Sidru/Cubet/Images/IMG_20200401_155650.jpg

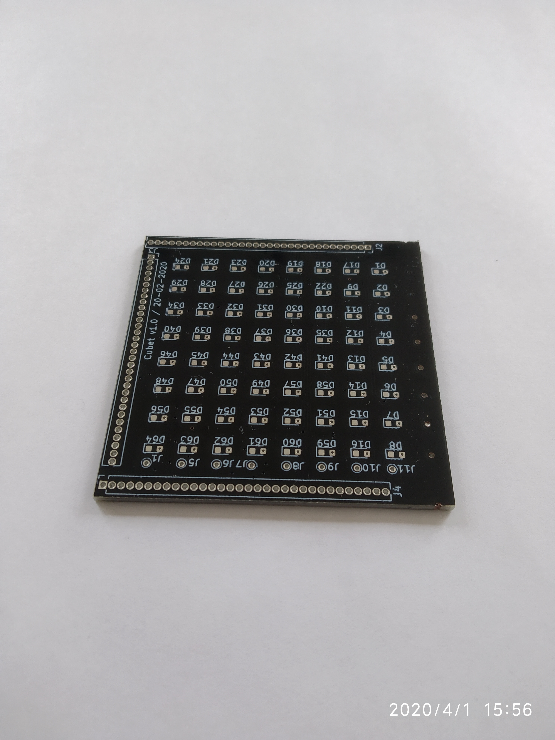
Images/IMG_20200401_155650.jpg
