Sidru/Cubet/Images/IMG_20200401_155713.jpg

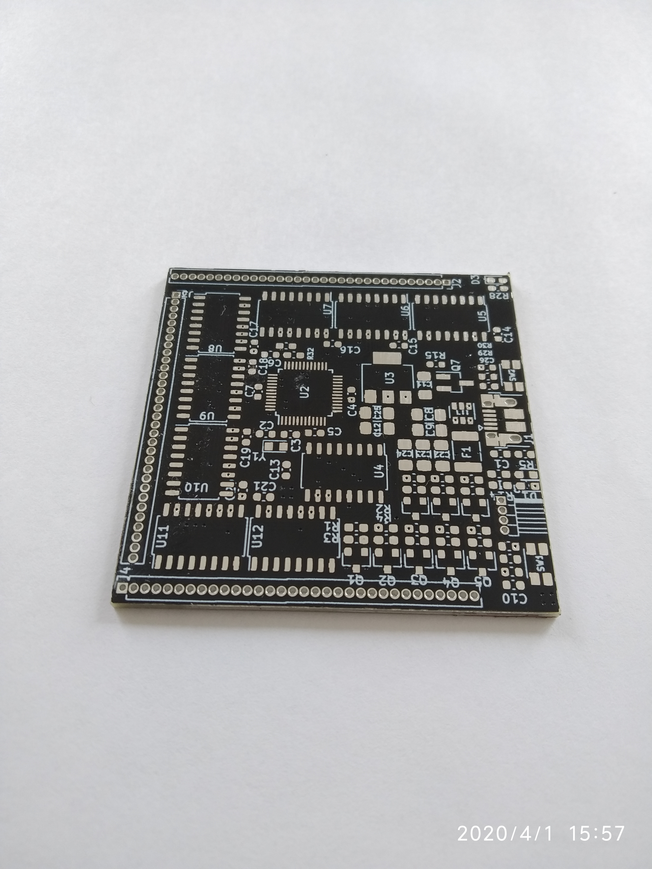
Images/IMG_20200401_155713.jpg
