Sidru/Cubet/Images/IMG_20200401_155931.jpg

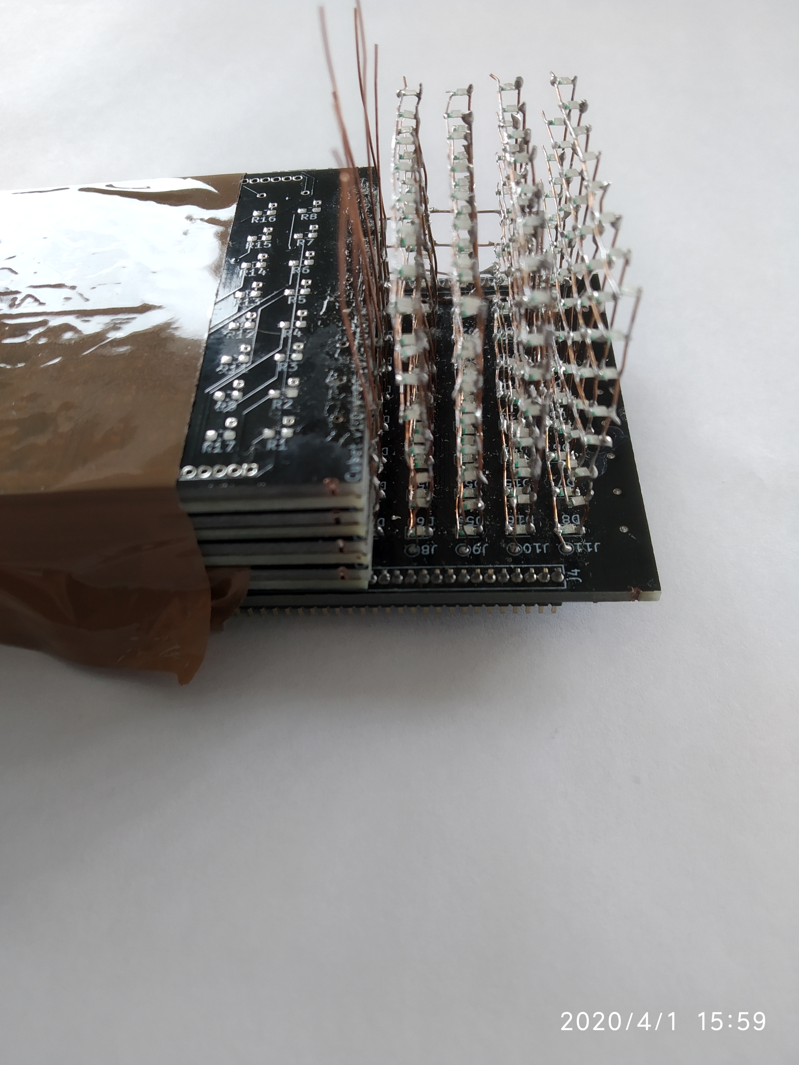
Images/IMG_20200401_155931.jpg
