Sidru/Cubet/Software/src/pinning.cpp

#include <Arduino.h>
#include <pinning.h>

/* Position from the columns in the shift array */
const uint8_t column_pos[8][8] = {
    {0,   1,  2,  3,  4,  5,  6,  7},
    {16, 8, 10, 11, 12, 13, 14, 15},
    {17, 21,  9, 34, 40, 57, 50, 58},
    {18, 24, 29, 35, 41, 56, 51, 59},
    {19, 25, 30, 36, 42, 48, 52, 60},
    {22, 26, 31, 37, 43, 49, 53, 61},
    {20, 27, 32, 38, 44, 46, 54, 62},
    {23, 28, 33, 39, 45, 47, 55, 63}
};
